lysolaka/QPoint/qpoint-firmware/src/display.rs

use embassy_stm32::gpio::Speed;
use embassy_stm32::i2c::{Config, I2c};
use embassy_stm32::pac::{GPIOB, gpio::vals::Idr};
use embassy_stm32::time::Hertz;

use display_interface::DisplayError;
use display_interface_i2c::I2CInterface;
use oled_async::Builder;
use oled_async::displays::sh1106::Sh1106_128_64;
use oled_async::prelude::*;

use qpoint_common::Parameter;

use crate::DisplayResources;
use crate::util::color;
use crate::util::display;
use crate::util::display::DisplayUpdate;
use crate::util::sync::ATTACHED_M;
use crate::util::sync::DISPLAY_UPDATE_Q;
use crate::util::sync::RGB_LED_S;

#[embassy_executor::task]
pub async fn driver(r: DisplayResources) -> ! {
    defmt::debug!("Configuring display driver...");
    let mut config = Config::default();
    config.frequency = Hertz::khz(400);
    config.gpio_speed = Speed::VeryHigh;

    let i2c = I2c::new(
        r.i2c,
        r.scl,
        r.sda,
        r.tx_dma,
        r.rx_dma,
        crate::Interrupts,
        config,
    );

    let interface = I2CInterface::new(i2c, 0x3c, 0x40);
    let mut display: GraphicsMode<_, _> = Builder::new(Sh1106_128_64 {})
        .with_rotation(DisplayRotation::Rotate180)
        .connect(interface)
        .into();

    let init: Result<(), DisplayError> = async {
        display.init().await?;
        display::clear(&mut display)?;

        // HACK: we don't know the initial state of the selection and to avoid a global variable and
        // polling, just directly read the GPIO IDR register.
        let selection = GPIOB.idr().read().idr(9) == Idr::HIGH;
        display::normal::draw_layout(&mut display)?;
        display::normal::draw_selection(&mut display, selection)?;
        display::normal::draw_drop(&mut display, 0.0)?;
        display::normal::draw_gain(&mut display, 0.0)?;

        display.flush().await?;
        Ok(())
    }
    .await;

    if let Err(e) = init {
        defmt::error!("Display driver: {}", e);
        defmt::warn!("The display driver is now useless");
        RGB_LED_S.signal(color::WARN);
        // this is needed because this function (task) never returns
        loop {
            // void the incoming display updates
            let _ = DISPLAY_UPDATE_Q.receive().await;
        }
    } else {
        defmt::info!("Display driver: OK!");
    }

    loop {
        let update = DISPLAY_UPDATE_Q.receive().await;
        // locking it for the entire update stops updates from conflicting
        let mut is_attached = ATTACHED_M.lock().await;
        if update.is_normal_mode() && *is_attached {
            defmt::warn!("Trying to execute a normal mode display update while attached, ignoring");
            continue;
        } else if !update.is_normal_mode() && !*is_attached {
            defmt::warn!(
                "Trying to execute an attached mode display update while not attached, ignoring"
            );
            continue;
        }

        let result: Result<(), DisplayError> = async {
            match update {
                DisplayUpdate::SetAttached => {
                    *is_attached = true;
                    display::clear(&mut display)?;
                    display::attached::draw_layout(&mut display)?;
                    display::attached::draw_parameter(&mut display, Parameter::Hie, 0.0)?;
                    display::attached::draw_parameter(&mut display, Parameter::Hre, 0.0)?;
                    display::attached::draw_parameter(&mut display, Parameter::Hfe, 0.0)?;
                    display::attached::draw_parameter(&mut display, Parameter::Hoe, 0.0)?;
                }
                DisplayUpdate::SetNormal => {
                    *is_attached = false;
                    display::clear(&mut display)?;
                    // HACK: we don't know the initial state of the selection and to avoid a global variable and
                    // polling, just directly read the GPIO IDR register.
                    let selection = GPIOB.idr().read().idr(9) == Idr::HIGH;
                    display::normal::draw_layout(&mut display)?;
                    display::normal::draw_selection(&mut display, selection)?;
                    display::normal::draw_drop(&mut display, 0.0)?;
                    display::normal::draw_gain(&mut display, 0.0)?;
                }
                DisplayUpdate::SetSelection(selection) => {
                    display::normal::draw_selection(&mut display, selection)?;
                }
                DisplayUpdate::SetDrop(drop) => {
                    display::normal::draw_drop(&mut display, drop)?;
                }
                DisplayUpdate::SetGain(gain) => {
                    display::normal::draw_gain(&mut display, gain)?;
                }
                DisplayUpdate::SetParameter { param, value } => {
                    display::attached::draw_parameter(&mut display, param, value)?;
                }
            }

            display.flush().await?;
            Ok(())
        }
        .await;

        if let Err(e) = result {
            defmt::error!("Display update failed: {}", e);
            RGB_LED_S.signal(color::ERR);
        }
    }
}
