lysolaka/QPoint/qpoint-firmware/src/util/color.rs

//! Colour constants for the RGB LED.

/// OK: green
pub const OK: (u8, u8, u8) = (0x1d, 0xdb, 0x0a);

/// WARN: yellow
pub const WARN: (u8, u8, u8) = (0xd9, 0xc2, 0x04);

/// ERR: red
pub const ERR: (u8, u8, u8) = (0xff, 0x05, 0x0f);

/// WAIT (Measurement in progress): blue
pub const WAIT: (u8, u8, u8) = (0x8b, 0xbf, 0xff);
